rbuwaENG/Atomatic_transfer_switch/pcb_design_kicad/src/img_1.png

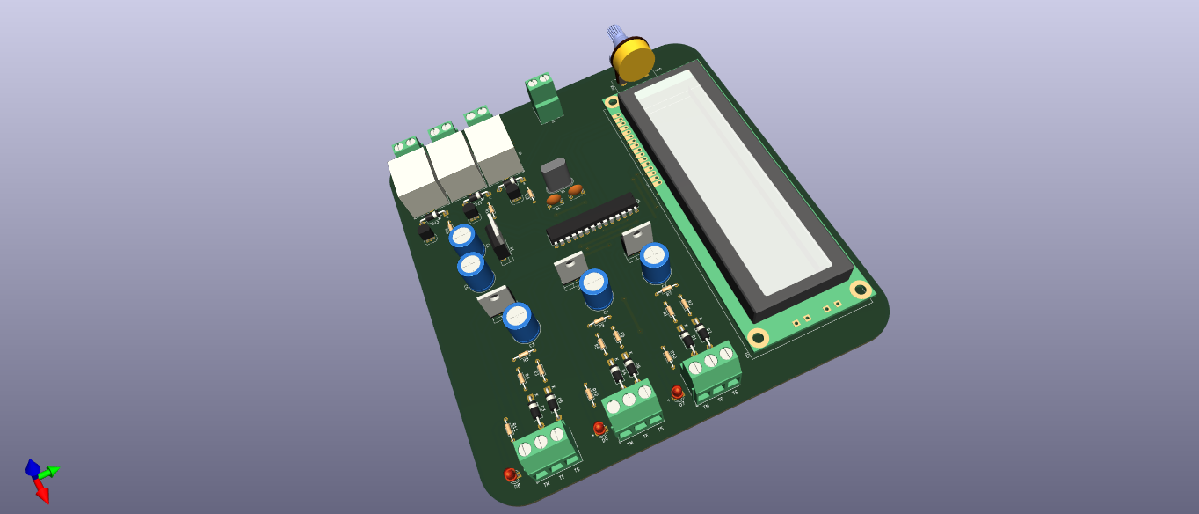
pcb_design_kicad/src/img_1.png
